jpetrocik/ucigate_mag/eepromburner/cadencepart2.h

const unsigned int cadence_start=32000;
const unsigned int cadence_length=17535;
const byte cadence[] PROGMEM = { 0x52, 0x49, 0x46, 0x46, 0x60, 0x5F, 0x00, 0x00, 0x57, 0x41, 0x56, 0x45, 0x66, 0x6D, 0x74, 0x20, 0x12, 0x00, 0x00, 0x00, 0x01, 0x00, 0x01, 0x00, 0x40, 0x1F, 0x00, 0x00, 0x40, 0x1F, 0x00, 0x00, 0x01, 0x00, 0x08, 0x00, 0x00, 0x00, 0x4C, 0x49, 0x53, 0x54, 0x80, 0x00, 0x00, 0x00, 0x49, 0x4E, 0x46, 0x4F, 0x49, 0x41, 0x52, 0x54, 0x0E, 0x00, 0x00, 0x00, 0x4A, 0x6F, 0x68, 0x6E, 0x20, 0x50, 0x65, 0x74, 0x72, 0x6F, 0x63, 0x69, 0x6B, 0x00, 0x49, 0x43, 0x52, 0x44, 0x11, 0x00, 0x00, 0x00, 0x32, 0x30, 0x31, 0x33, 0x2D, 0x31, 0x30, 0x2D, 0x31, 0x33, 0x20, 0x32, 0x32, 0x3A, 0x32, 0x39, 0x00, 0x00, 0x49, 0x4E, 0x41, 0x4D, 0x0F, 0x00, 0x00, 0x00, 0x63, 0x61, 0x64, 0x65, 0x6E, 0x63, 0x65, 0x2D, 0x70, 0x61, 0x72, 0x74, 0x2D, 0x32, 0x00, 0x00, 0x49, 0x50, 0x52, 0x44, 0x16, 0x00, 0x00, 0x00, 0x4A, 0x6F, 0x68, 0x6E, 0x20, 0x50, 0x65, 0x74, 0x72, 0x6F, 0x63, 0x69, 0x6B, 0x27, 0x73, 0x20, 0x41, 0x6C, 0x62, 0x75, 0x6D, 0x00, 0x49, 0x53, 0x46, 0x54, 0x0E, 0x00, 0x00, 0x00, 0x4C, 0x61, 0x76, 0x66, 0x35, 0x34, 0x2E, 0x36, 0x33, 0x2E, 0x31, 0x30, 0x34, 0x00, 0x64, 0x61, 0x74, 0x61, 0xB2, 0x5E, 0x00, 0x00, 0x80, 0x80, 0x80, 0x80, 0x80, 0x80, 0x80, 0x80, 0x80, 0x80, 0x80, 0x80, 0x80, 0x80, 0x80, 0x80, 0x80, 0x80, 0x80, 0x80, 0x80, 0x80, 0x80, 0x80, 0x80, 0x80, 0x80, 0x80, 0x80, 0x80, 0x80, 0x80, 0x80, 0x80, 0x80, 0x80, 0x80, 0x80, 0x80, 0x80, 0x80, 0x80, 0x80, 0x80, 0x80, 0x80, 0x80, 0x7F, 0x80, 0x80, 0x80, 0x80, 0x7F, 0x80, 0x80, 0x7F, 0x7F, 0x80, 0x7F, 0x80, 0x80, 0x7F, 0x8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
0, 0x80, 0x80, 0x80, 0x80, 0x80, 0x80, 0x80, 0x80, 0x80, 0x80, 0x80, 0x80, 0x80, 0x80, 0x80, 0x80, 0x80, 0x80, 0x80, 0x80, 0x80, 0x80, 0x80, 0x80, 0x80, 0x80, 0x80, 0x80, 0x80, 0x80, 0x80, 0x80, 0x80, 0x80, 0x80, 0x80, 0x80, 0x80, 0x80, 0x80, };
